NotoFederico/FuncGen/FuncGen_ESP8266/data/imagen.png

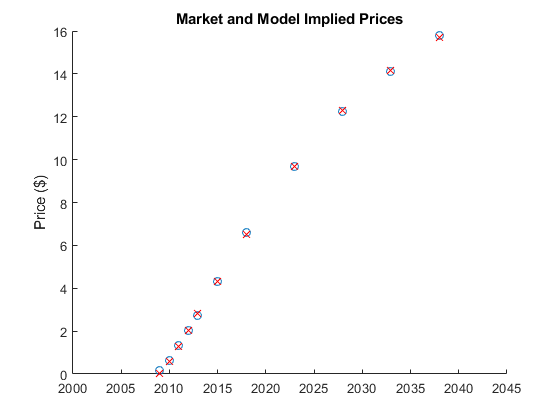
FuncGen_ESP8266/data/imagen.png
