NotoFederico/FuncGen/FuncGen_Simulation/4051HierTesti.asc

RL: res; 33k; tol=1 pwr=0.1
U1: CD4024B; VDD={Vcc}  SPEED=1.0  TRIPDT=5e-9
V0: voltage; SINE({Vcc/2} {Vcc/2-1} {Fin})
V1: voltage; SINE({Vcc/2} {Vcc/2-1} {Fin+K})
V2: voltage; SINE({Vcc/2} {Vcc/2-1} {Fin+K*2})
V3: voltage; SINE({Vcc/2} {Vcc/2-1} {Fin+K*3})
V4: voltage; SINE({Vcc/2} {Vcc/2-1} {Fin+K*4})
V5: voltage; SINE({Vcc/2} {Vcc/2-1} {Fin+K*5})
V6: voltage; SINE({Vcc/2} {Vcc/2-1} {Fin+K*6})
V7: voltage; SINE({Vcc/2} {Vcc/2-1} {Fin+K*7})
Vcc: voltage; {Vcc}; Rser=10 Cpar=1u
Vclk: voltage; PULSE(0 {Vcc} 1m 1u 1u 500u 1m); Rser=1
X1: 4051
Named nets: 0, IO2, IO1, IO0, IO3, A, B, C, IOC, IO6, IO4, IO7, IO5, Vss, V+
.param Vcc=15 Vel=1 Fin=1k K=1k
.tran 8m
.option noopiter
