NotoFederico/FuncGen/FuncGen_Simulation/electronica.asc

C1: cap; 100µ
D1: zener; BZX384B5V1
D2: zener; BZX384B5V1
D3: diode; 1N4007
D4: diode; 1N4007
J2: njf; BF245B
R1: res; 5.6k; tol=10
R2: res; 33k; tol=10
R3: res; 10k; tol=10
R4: res; 50k; tol=10
R5: res; 50k; tol=10
R6: res; 50k; tol=10
R7: res; 50k; tol=10
R8: res; 75k
R9: res; 25k; tol=10
R10: res; 47k; tol=10
R11: res; 47k; tol=10
R12: res; 10k; tol=10
R13: res; 10k; tol=10
R14: res; 10k; tol=10
R15: res; 10k; tol=10
R16: res; 1000
R17: res; 10k; tol=10
R18: res; 10k; tol=10
R19: res; 3.3k; tol=10
R20: res; 10k; tol=10
R21: res; 3.3k; tol=10
R22: res; 8.2k; tol=10
R23: res; 8.2k; tol=10
R24: res; 10k
R25: res; 2.7k
R26: res; 10k
R27: res; 33k
R28: res; 10k
R29: res; 2.7k
R30: res; 10k
R31: res; 33k
R32: res; 10k
R35: res; 10k
R36: res; 10k
U1: TL072
U2: TL072
U3: TL072
U4: TL072
U5: TL072
U6: TL072
U7: TL072
U8: TL072
V1: voltage; 3.3
V2: voltage; SINE(1.65 1.65 10); AC 1
V3: voltage; -12
V4: voltage; +12
V5: voltage; PULSE(0 1 1p 1p 1p 2.5m 5m); AC 1
V6: voltage; -12
V7: voltage; 12
V8: voltage; 5V
V11: voltage; 0
V12: voltage; 5
V13: voltage; 3.3
X2: 4051
Named nets: 0, Offset, Amp, Output, Offset_ADC, Amplitude_ADC, -12, +12, +5V, A
.lib opamp.sub
.tran 0.1
;ac dec .10000 0.1 10000000
De 0 a 2047 el offset es negativo
De 2048 a 4095 el offset es positivo
.param Vcc=5 Vel=1 Fin=1k K=1k
