NotoFederico/FuncGen/FuncGen_Simulation/4051.asc

S0: sw
S1: sw
S2: sw
S3: sw
S4: sw
S5: sw
S6: sw
S7: sw
U1: 3to8l; VDD={Vcc}  SPEED=1.0  TRIPDT=5e-9
Named nets: IO0, V+, IO1, Y0, Y1, Y2, Y3, Y4, Y5, Y6, Y7, A, B, C, INH, Vss, Vee, IOC, IO2, IO3, IO4, IO5, IO6, IO7
13
14
15
3
11
10
9
6
8
7
.model Sw Sw(Ron=1e2 Roff=1e9 Vt={Vcc/2} Vh=1m)
12
1
5
2
4
16
